aaroneiche/macsao/firmware/macsao/tiles.h

static const unsigned char grey[] = {
    0x55, 0xaa, 0x55, 0xaa, 0x55, 0xaa, 0x55, 0xaa};

static const unsigned char scrollbar_back[] = {
    0xaa, 0xff, 0x55, 0x00, 0x00, 0x00, 0x00, 0x00};

// static const unsigned char disk[] = {
//     0x03, 0x49, 0x42, 0x42, 0x7e, 0x42, 0x5a, 0x00};

// static const unsigned char disk[] = {
//     0x40, 0x92, 0x42, 0x42, 0x7e, 0x42, 0x5a, 0x00};

// static const unsigned char diskOpen[] = {
//     0x40, 0xba, 0x6e, 0x3a, 0x6e, 0x3a, 0x6e, 0x00, 
// };

// Good
static const unsigned char diskB[] = {
    0xc0, 0x92, 0x42, 0x42, 0x7e, 0x42, 0x5a, 0x00};
// Good
static const unsigned char diskW[] = {
    0x00, 0x48, 0x42, 0x42, 0x7e, 0x42, 0x5a, 0x00};


static const unsigned char diskSelectedB[] = {
    0xff, 0xed, 0xbd, 0xbd, 0x81, 0xbd, 0xa5, 0xff};

static const unsigned char diskSelectedW[] = {
    0x3f, 0x6d, 0xbd, 0xbd, 0x81, 0xbd, 0xa5, 0xff};

//test
static const unsigned char diskOpenB[] = {
    // 0xc0, 0x94, 0x2a, 0x54, 0x2a, 0x54, 0x2a, 0x00
    0xc0, 0x9c, 0x76, 0x5c, 0x76, 0x5c, 0x76, 0x00
};
//test
static const unsigned char diskOpenW[] = {
    // 0x00, 0x14, 0x2a, 0x54, 0x2a, 0x54, 0x2a, 0x00    
    0x00, 0x1c, 0x76, 0x5c, 0x76, 0x5c, 0x76, 0x00
};

static const unsigned char diskOpenSelectedW[] = {
    0x00, 0x02, 0x08, 0x22, 0x08, 0x22, 0x08, 0x00 
};

static const unsigned char diskOpenSelectedB[] = {
    0xc0, 0x82, 0x08, 0x22, 0x08, 0x22, 0x08, 0x00
};



static const unsigned char appIcon[] = {0xe7, 0xdb, 0xbd, 0x66, 0x46, 0xad, 0x4b, 0x17};

static const unsigned char appIcon2[] = {
    0xe7, 0xdb, 0xad, 0x66, 0x46, 0xb5, 0x6b, 0x17 };

static const unsigned char folder[] = {
0x03, 0x79, 0x79, 0x79, 0x7b, 0x7b, 0x7b, 0x03};

static const unsigned char pointer[] = {
    // 0x7f, 0x3f, 0x3f, 0xbf, 0xff, 0xff, 0xff, 0xff
    0x01, 0x03, 0x03, 0x02, 0x00, 0x00, 0x00, 0x00};
static const unsigned char pointerOutline[] = {
    // 0xbf, 0x5f, 0x6f, 0xaf, 0xdf, 0xff, 0xff, 0xff
    0xfc, 0xfa, 0xf6, 0xf5, 0xfb, 0xff, 0xff, 0xff
};

static const unsigned char wrencher[] = {
    0x38, 0x00, 0x1c, 0x1c, 0x00, 0x38, 0x8c, 0x00, 0x31, 0xcc, 0x00, 0x33, 0xfe, 0x7e, 0x7f, 0x7c,
    0xff, 0x3e, 0x09, 0xff, 0x90, 0x01, 0xff, 0x80, 0x01, 0xff, 0xc0, 0x03, 0x99, 0xc0, 0x03, 0x18,
    0xc0, 0x03, 0x18, 0xc0, 0x03, 0x3c, 0xc0, 0x03, 0xff, 0xc0, 0x03, 0xe7, 0xc0, 0x03, 0xff, 0xc0,
    0x01, 0xff, 0x80, 0x08, 0xff, 0x10, 0x7c, 0xdb, 0x3e, 0xfe, 0x00, 0x7f, 0xcc, 0x00, 0x33, 0x8c,
    0x00, 0x31, 0x1c, 0x00, 0x38, 0x38, 0x00, 0x1c};

static const unsigned char happyMac[] = {
    0x01, 0xfe, 0x06, 0xfa, 0x6a, 0xfa, 0x9a, 0xfa, 0x6a, 0xfa, 0x06, 0xfe, 0x01, 0xff, 0xff, 0xff,
    0xc0, 0x1f, 0x5c, 0x4b, 0x5b, 0x5a, 0x5a, 0x5a, 0x4b, 0x4b, 0x5c, 0x1f, 0xc0, 0xff, 0xff, 0xff
};
